TheAngryRaven/DovesDataLogger/CASE/VER_1/STEP/screen-cutout-template.STEP

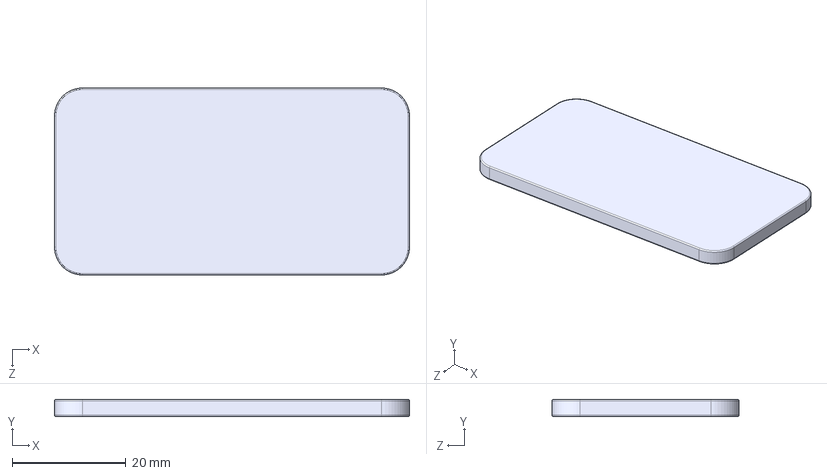
[picture p26: CAD file, 2026-03-16]
CASE/VER_1/STEP/screen-cutout-template.STEP
62.3 x 3.00 x 32.8 mm
