TheAngryRaven/DovesDataLogger/CASE/3MF/GPS-HOLDER.3MF

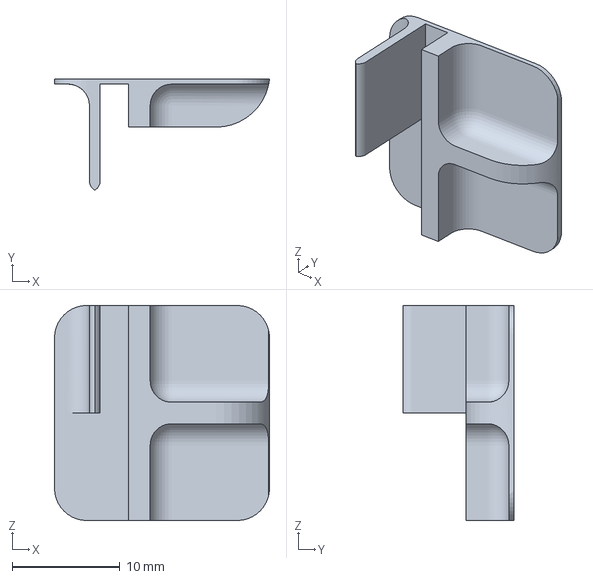
[picture p27: CAD file, 2026-07-27]
CASE/3MF/GPS-HOLDER.3MF
20.0 x 10.4 x 20.0 mm
