TheAngryRaven/DovesDataLogger/CASE/VER_1/STEP/switch-cover.STEP

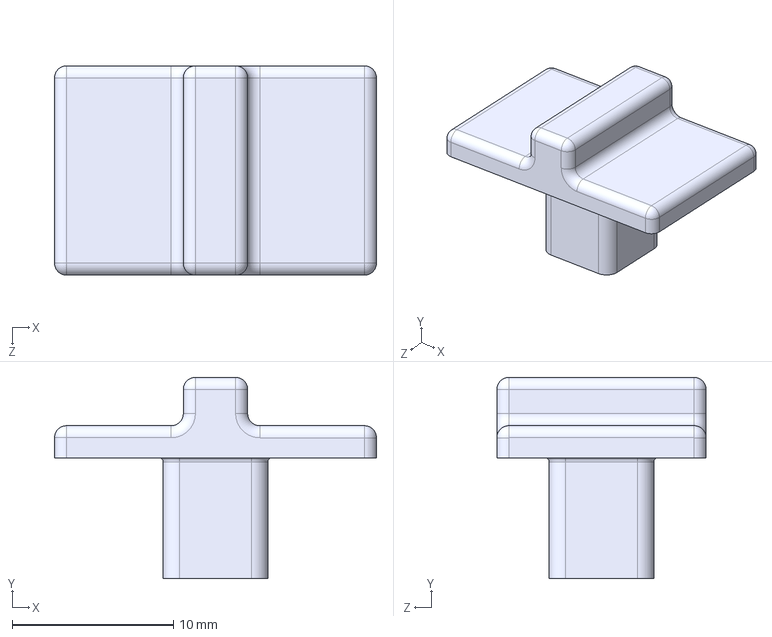
[picture p28: CAD file, 2026-03-16]
CASE/VER_1/STEP/switch-cover.STEP
20.0 x 12.5 x 13.0 mm
