TheAngryRaven/DovesDataLogger/CASE/3MF/cpu-lid.3MF

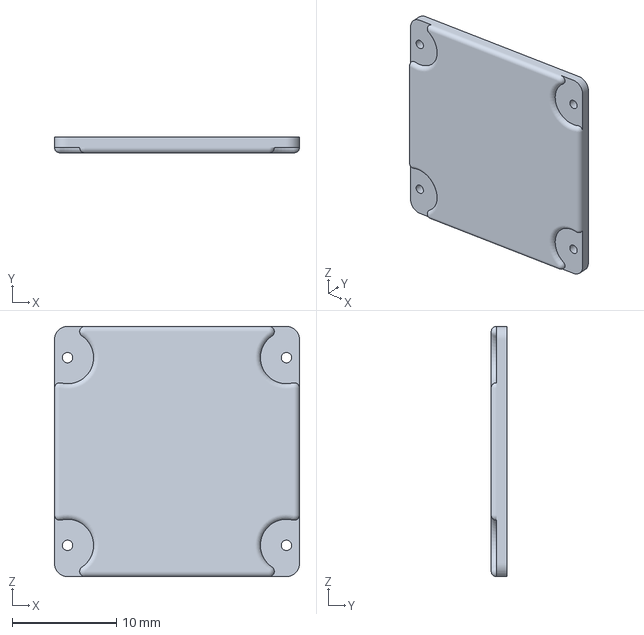
[picture p29: CAD file, 2026-07-27]
CASE/3MF/cpu-lid.3MF
23.5 x 1.50 x 24.0 mm
