TheAngryRaven/DovesDataLogger/CASE/VER_1/STEP/battery-lid.STEP

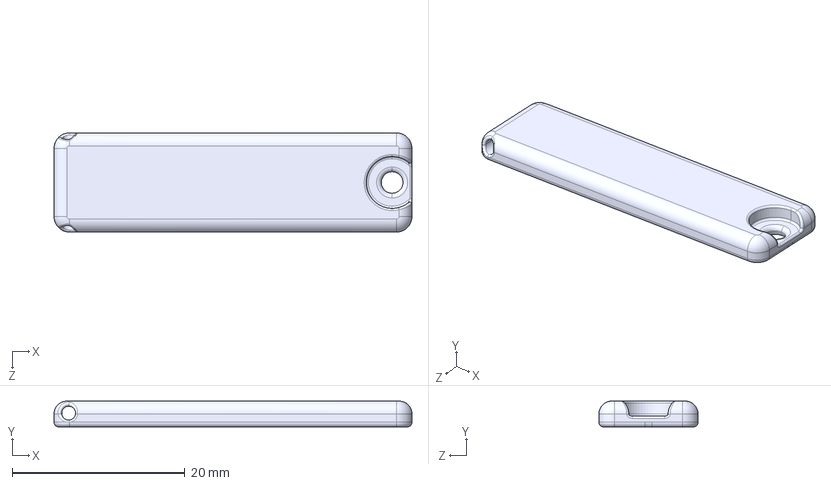
[picture p30: CAD file, 2026-03-16]
CASE/VER_1/STEP/battery-lid.STEP
41.5 x 3.00 x 11.5 mm
