TheAngryRaven/DovesDataLogger/CASE/3MF/diy-gps.3MF

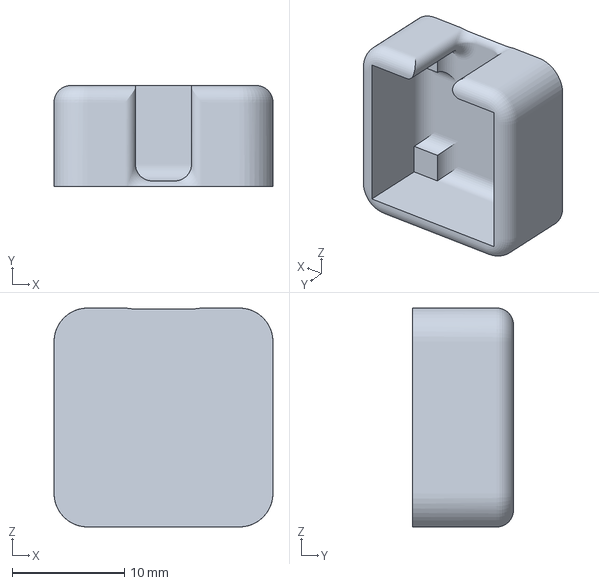
[picture p31: CAD file, 2026-07-27]
CASE/3MF/diy-gps.3MF
19.5 x 9.00 x 19.5 mm
