TheAngryRaven/DovesDataLogger/CASE/VER_1/STEP/sdcard.STEP

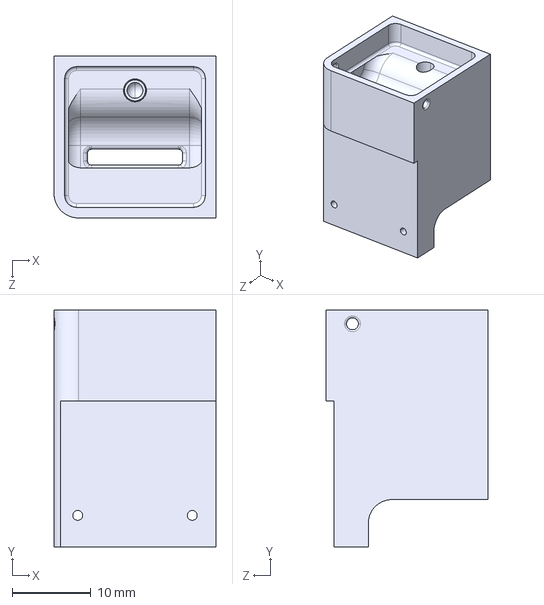
[picture p32: CAD file, 2026-03-16]
CASE/VER_1/STEP/sdcard.STEP
20.5 x 30.0 x 20.5 mm
