TheAngryRaven/DovesDataLogger/CASE/3MF/usbc_charger.3MF

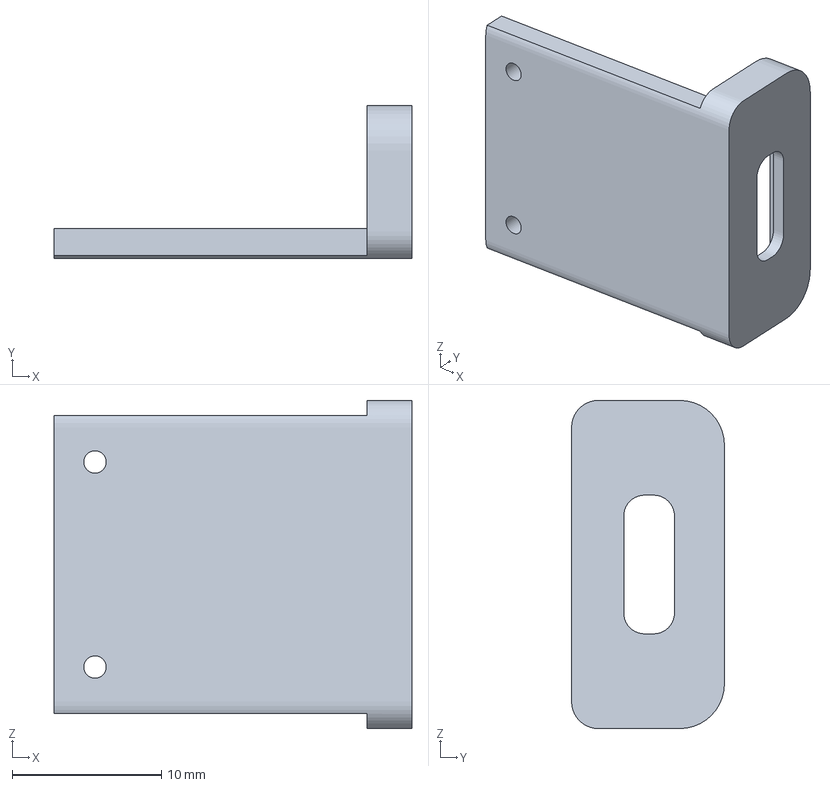
[picture p33: CAD file, 2026-07-27]
CASE/3MF/usbc_charger.3MF
24.0 x 10.2 x 22.0 mm
