TheAngryRaven/DovesDataLogger/CASE/VER_1/STEP/gps.STEP

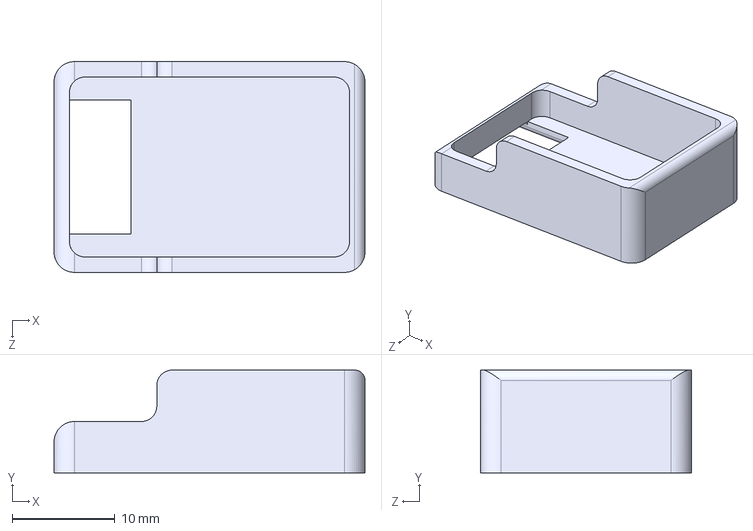
[picture p34: CAD file, 2026-03-16]
CASE/VER_1/STEP/gps.STEP
30.2 x 10.0 x 20.5 mm
