TheAngryRaven/DovesDataLogger/CASE/3MF/cpu.3MF

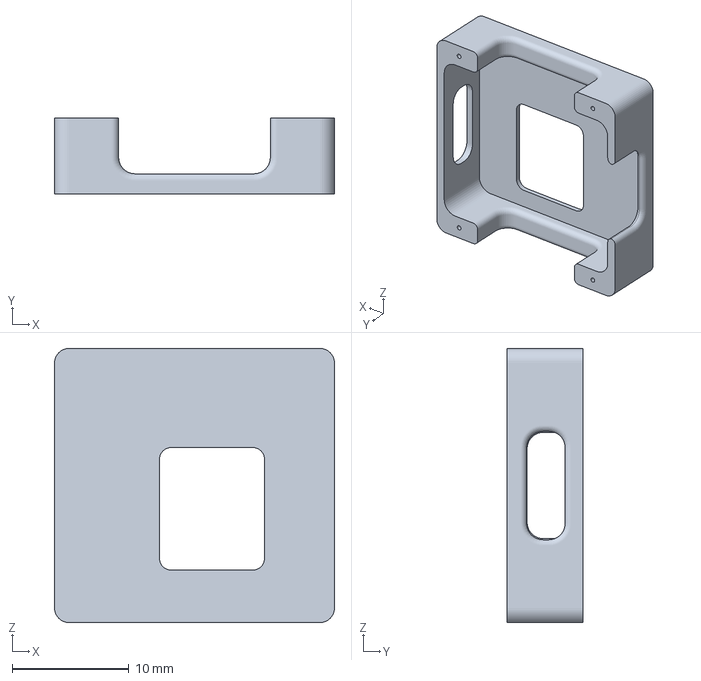
[picture p35: CAD file, 2026-07-27]
CASE/3MF/cpu.3MF
24.0 x 6.55 x 23.5 mm
