TheAngryRaven/DovesDataLogger/BirdsEye/gps_functions.ino

///////////////////////////////////////////
// GPS MODULE
// GPS time functions, configuration, setup, main loop, and frame rate
// Uses SparkFun u-blox GNSS v3 library with UBX PVT binary protocol
///////////////////////////////////////////

#include "gps_functions.h"
#include "gps_stats.h"
#include "gps_time.h"
#include "gps_validation.h"
#include "nan_bits.h"
#include "sat_bars.h"

///////////////////////////////////////////
// GPS SERIAL BUFFER — two buffers, two failure modes
//
// UARTE0 (per-byte ISR, NVIC prio 3) → core RingBuffer (256 B via the
// SERIAL_BUFFER_SIZE build flag; project.h asserts it) → TIMER3 ISR
// (prio 3, every GPS_DRAIN_INTERVAL_US) → this 4 KB ring → SparkFun
// library via GpsBufferedStream on the main loop.
//
// Downstream stalls (SD garbage collection blocks the main loop
// 100 ms–2 s): the 4 KB ring buffers ~1.6 s of stream while TIMER3
// keeps draining — the original reason this ISR exists.
//
// Upstream deferral (SoftDevice radio ISRs at prio 0–2 preempt both
// prio-3 ISRs): only the CORE ring absorbs bytes until TIMER3 gets to
// run. 256 B ≈ 44 ms of line rate at 57600 baud, so radio activity
// (SensorEgg scan windows, camera connection events) has huge margin
// before a byte is lost. Both overflow points are counted — see the
// gpsStats* accessors and the GPS debug page.
///////////////////////////////////////////

// Forward-declare ISR with C linkage BEFORE Arduino's preprocessor
// auto-generates a C++ prototype (which would conflict with extern "C").
extern "C" void TIMER3_IRQHandler(void);

#define GPS_RX_BUF_SIZE 4096
static uint8_t gpsRxBuf[GPS_RX_BUF_SIZE];
static volatile uint16_t gpsRxHead = 0;  // Written by ISR only
static volatile uint16_t gpsRxTail = 0;  // Read by main loop only (via gpsStream)
static volatile bool gpsTimerActive = false;

// Serial-pipeline health counters (monotonic since boot, read via the
// gpsStats*() accessors, shown on the GPS debug page). ISR writes are a
// few cycles each; no SVCs, no floats.
static volatile uint32_t gpsRingFullEvents = 0;   // 4KB ring full at drain time
static volatile uint32_t gpsIsrLatencyMaxUs = 0;  // worst TIMER3 fire→entry deferral
static volatile uint16_t gpsDrainMaxBytes = 0;    // biggest single-fire drain burst
static volatile uint32_t gpsCoreSatEvents = 0;    // drain burst filled the core RX ring
static gps_stats::DropMonitor gpsDropMonitor;     // main-loop only (frame-rate window)

// Stream wrapper: SparkFun library reads from our 4KB buffer instead of Serial1.
// Before the timer ISR is started (during GPS_SETUP), reads pass through to
// GPS_SERIAL directly so that myGNSS.begin() can communicate with the module.
class GpsBufferedStream : public Stream {
public:
  int available() override {
    if (!gpsTimerActive) return GPS_SERIAL.available();
    return (GPS_RX_BUF_SIZE + gpsRxHead - gpsRxTail) % GPS_RX_BUF_SIZE;
  }
  int read() override {
    if (!gpsTimerActive) return GPS_SERIAL.read();
    if (gpsRxHead == gpsRxTail) return -1;
    uint8_t c = gpsRxBuf[gpsRxTail];
    gpsRxTail = (gpsRxTail + 1) % GPS_RX_BUF_SIZE;
    return c;
  }
  int peek() override {
    if (!gpsTimerActive) return GPS_SERIAL.peek();
    if (gpsRxHead == gpsRxTail) return -1;
    return gpsRxBuf[gpsRxTail];
  }
  size_t write(uint8_t c) override {
    return GPS_SERIAL.write(c);
  }
  size_t write(const uint8_t *buffer, size_t size) override {
    return GPS_SERIAL.write(buffer, size);
  }
  void flush() override {
    GPS_SERIAL.flush();
  }
};

static GpsBufferedStream gpsStream;

// Timer3 ISR: drains Serial1 into our 4KB buffer every ~10ms.
// Single-producer (ISR writes gpsRxHead), single-consumer (main loop
// reads gpsRxTail via gpsStream) — lock-free ring buffer.
//
// Brief __disable_irq() around each GPS_SERIAL read protects the UART
// driver's internal FIFO from concurrent access by the core's UARTE
// ISR (same NVIC priority 3 as this handler, so it can't preempt us —
// the guard covers it firing *between* our read calls). Each critical
// section is ~0.3µs — well within SoftDevice's 6µs safe window.
void TIMER3_IRQHandler(void) {
  if (NRF_TIMER3->EVENTS_COMPARE[0]) {
    NRF_TIMER3->EVENTS_COMPARE[0] = 0;
    // The COMPARE0_CLEAR short zeroed the counter at the scheduled fire
    // time, so capturing now reads how long SoftDevice radio ISRs (the
    // only thing above priority 3) deferred this handler, in µs. If a
    // deferral swallows a whole period the reading wraps mod the period
    // — the drain/saturation counters below catch that case.
    NRF_TIMER3->TASKS_CAPTURE[1] = 1;
    uint32_t deferralUs = NRF_TIMER3->CC[1];
    if (deferralUs > gpsIsrLatencyMaxUs) gpsIsrLatencyMaxUs = deferralUs;
    uint16_t drained = 0;
    while (true) {
      __disable_irq();
      int c = GPS_SERIAL.available() ? GPS_SERIAL.read() : -1;
      __enable_irq();
      if (c < 0) break;

      uint16_t nextHead = (gpsRxHead + 1) % GPS_RX_BUF_SIZE;
      if (nextHead == gpsRxTail) {  // Buffer full, drop bytes
        gpsRingFullEvents++;
        break;
      }
      gpsRxBuf[gpsRxHead] = (uint8_t)c;
      gpsRxHead = nextHead;
      drained++;
    }
    if (drained > gpsDrainMaxBytes) gpsDrainMaxBytes = drained;
    // Draining a full core ring means it was saturated while we were
    // deferred — bytes may already have been dropped upstream (the
    // core's store_char discards silently on full).
    if (drained >= SERIAL_BUFFER_SIZE - 1) gpsCoreSatEvents++;
  }
}

void startGpsSerialTimer() {
  NRF_TIMER3->TASKS_STOP = 1;
  NRF_TIMER3->TASKS_CLEAR = 1;
  NRF_TIMER3->MODE = TIMER_MODE_MODE_Timer;
  NRF_TIMER3->BITMODE = TIMER_BITMODE_BITMODE_32Bit;
  NRF_TIMER3->PRESCALER = 4;              // 16MHz / 2^4 = 1MHz tick
  NRF_TIMER3->CC[0] = GPS_DRAIN_INTERVAL_US;  // drain period (see gps_config.h)
  NRF_TIMER3->SHORTS = TIMER_SHORTS_COMPARE0_CLEAR_Msk;
  NRF_TIMER3->INTENSET = TIMER_INTENSET_COMPARE0_Msk;
  NVIC_SetPriority(TIMER3_IRQn, 3);       // Below SoftDevice (0-2), above main loop
  NVIC_ClearPendingIRQ(TIMER3_IRQn);      // Clear stale pending interrupt from prior session
  NVIC_EnableIRQ(TIMER3_IRQn);
  gpsTimerActive = true;
  NRF_TIMER3->TASKS_START = 1;
  debugln(F("GPS serial buffer timer started"));
}

void stopGpsSerialTimer() {
  NRF_TIMER3->TASKS_STOP = 1;
  NRF_TIMER3->INTENCLR = TIMER_INTENCLR_COMPARE0_Msk;
  NVIC_DisableIRQ(TIMER3_IRQn);
  NVIC_ClearPendingIRQ(TIMER3_IRQn);      // Ensure no stale ISR fires after disable
  __DSB();                                 // ARM barrier: NVIC ops complete before flag update
  gpsTimerActive = false;
}

/**
  * @brief Returns the GPS time since midnight in milliseconds, or 0 if GPS unavailable.
  *        The pure math lives in gps_time::timeOfDayMs — this just plumbs through gpsData.
  */
unsigned long getGpsTimeInMilliseconds() {
  if (!gpsInitialized) return 0;
  return gps_time::timeOfDayMs(gpsData.hour, gpsData.minute,
                               gpsData.seconds, gpsData.milliseconds);
}

/**
  * @brief Converts GPS date/time to Unix timestamp in seconds. 0 if GPS unavailable.
  *        gpsData.year is the 2-digit year offset from 2000.
  */
unsigned long getGpsUnixTimestamp() {
  if (!gpsInitialized) return 0;
  return static_cast<unsigned long>(gps_time::unixTimestampSeconds(
      2000 + gpsData.year, gpsData.month, gpsData.day,
      gpsData.hour, gpsData.minute, gpsData.seconds));
}

/**
  * @brief Converts GPS date/time to Unix timestamp with millisecond precision.
  *        0 if GPS unavailable.
  */
unsigned long long getGpsUnixTimestampMillis() {
  if (!gpsInitialized) return 0;
  return gps_time::unixTimestampMillis(
      2000 + gpsData.year, gpsData.month, gpsData.day,
      gpsData.hour, gpsData.minute, gpsData.seconds, gpsData.milliseconds);
}

// PVT callback — called synchronously from checkCallbacks() when a new
// NAV-PVT message arrives.  Populates the shared gpsData struct and sets
// the gpsDataFresh flag so GPS_LOOP() knows to run lap-timer / logging.
void onPVTReceived(UBX_NAV_PVT_data_t *pvt) {
  // lat/lng stay double (see GpsData); the rest is single-precision with
  // reciprocal-constant multiplies — hardware FPU, no software-double
  // divides in this 25 Hz callback.
  gpsData.latitudeDegrees = pvt->lat / 1e7;
  gpsData.longitudeDegrees = pvt->lon / 1e7;
  gpsData.altitude = (float)pvt->hMSL * 0.001f;            // mm → meters
  gpsData.speed = (float)pvt->gSpeed * (1.0f / 514.444f);  // mm/s → knots
  gpsData.HDOP = (float)pvt->pDOP * 0.01f;                 // pDOP ≈ HDOP for track use
  gpsData.heading = (float)pvt->headMot * 1e-5f;           // deg * 1e-5 → degrees
  gpsData.horizontalAccuracy = (float)pvt->hAcc * 0.001f;  // mm → meters
  gpsData.satellites = pvt->numSV;
  // A fix is only trustworthy when the module also asserts gnssFixOK — a bare
  // fixType >= 2 can appear during convergence with garbage coordinates.
  gpsData.fix = (pvt->fixType >= 2) && (pvt->flags.bits.gnssFixOK != 0);
  // Time is only usable for naming/saving the log once the module reports the
  // date AND time AND a fully-resolved UTC. Before this, the module emits a
  // placeholder date (e.g. 2021-03-07) that must NOT drive file creation.
  gpsData.timeDateValid = (pvt->valid.bits.validDate != 0) &&
                          (pvt->valid.bits.validTime != 0);
  gpsData.timeResolved = (pvt->valid.bits.fullyResolved != 0);
  gpsData.timeValid = gpsData.timeDateValid && gpsData.timeResolved;
  gpsData.year = pvt->year - 2000;
  gpsData.month = pvt->month;
  gpsData.day = pvt->day;
  gpsData.hour = pvt->hour;
  gpsData.minute = pvt->min;
  gpsData.seconds = pvt->sec;
  gpsData.milliseconds = (pvt->iTOW % 1000);       // ms from GPS time-of-week

  gpsDataFresh = true;
  gpsPvtSequence++;  // monotonic; for consumers that run after GPS_LOOP()
  gpsFrameCounter++;
}

// NAV-SAT callback — fired by checkCallbacks() while status mode has
// NAV-SAT enabled. Snapshots per-satellite CNO (used-in-nav first,
// strongest first — rules in the host-tested sat_bars unit) for the GPS
// status page's signal bars.
void onNAVSATReceived(UBX_NAV_SAT_data_t *sat) {
  sat_bars::SatObs obs[64];
  uint8_t n = sat->header.numSvs;
  if (n > 64) n = 64;
  uint8_t used = 0;
  uint8_t tracked = 0;
  for (uint8_t i = 0; i < n; i++) {
    obs[i].cno = sat->blocks[i].cno;
    obs[i].used = (sat->blocks[i].flags.bits.svUsed != 0);
    if (obs[i].used) used++;
    if (obs[i].cno > 0) tracked++;  // hearing a signal, used in nav or not
  }
  gpsSatUsedCount = used;
  gpsSatTrackedCount = tracked;
  gpsSatCnoCount = (uint8_t)sat_bars::selectCnos(obs, n, gpsSatCnos,
                                                 sat_bars::kMaxSats);
}

// Register the message callbacks with the SparkFun library. Needed
// after every myGNSS.begin() — begin() resets library state, dropping
// previously registered callbacks.
static void gpsRegisterCallbacks() {
  // Runs under the armed WDT when re-registering after a baud recovery —
  // each call is a blocking VALSET/ACK exchange (see GPS_RECONFIGURE).
  wdtPet();
  myGNSS.setAutoPVTcallbackPtr(&onPVTReceived);
  wdtPet();
  if (gpsNavSatWanted) {
    myGNSS.setAutoNAVSATcallbackPtr(&onNAVSATReceived);
    wdtPet();
    // NAV-SAT frames are big (8 + 12*numSvs bytes); divide them down to
    // ~1 Hz instead of one per nav solution. Plenty for signal bars.
    myGNSS.setAutoNAVSATrate(GPS_NAV_RATE_STATUS_HZ);
    wdtPet();
  }
}

// Serial1 open-state guard for baud switches. The core's Uart::end()
// spin-waits on the TXSTOPPED + RXTO events, but a never-begun UARTE is
// disabled and ignores the STOPRX/STOPTX task writes — the events can
// never fire and end() loops forever. (end() has no _begun check; begin()
// does, and is a no-op on an open port, so a baud change NEEDS the end().)
// Track open state ourselves and only end() a port we actually opened.
static bool gpsSerialBegun = false;
static void gpsSerialRestart(unsigned long baud) {
  if (gpsSerialBegun) {
    GPS_SERIAL.end();
    delay(20);
  }
  GPS_SERIAL.begin(baud);
  gpsSerialBegun = true;
}

// The baud probe ladder. The module can be in ANY state at boot — every
// boot is a cold start now that sleep is System OFF:
//   (1) software backup mode holding a 57600 config (the normal wake),
//   (2) already-configured 57600 and running (MCU-only reset: reboot
//       combo, watchdog, OTA),
//   (3) factory 9600 NMEA (true cold power, or V_BCKP/VCC brownout).
// Sequence: backup-wake byte first (harmless if awake), probe 57600
// (the common warm case, ~instant), fall back to 9600 + rate switch,
// and only if all that fails pay a cold-boot delay and retry once.
// Caller owns gpsInitialized and the serial timer.
static bool gpsSetupProbe(bool coldRetry) {
  // Any UART activity on RX wakes u-blox from powerOff backup mode.
  gpsSerialRestart(GPS_BAUD_RATE);
  delay(50);
  GPS_SERIAL.write(0xFF);
  delay(100);

  // 57600 first — warm module answers immediately. Short maxWait: a
  // failing begin() is 3 internal ping retries back-to-back with no way
  // to pet the WDT in between (see GPS_PROBE_MAXWAIT_MS).
  wdtPet();
  if (myGNSS.begin(gpsStream, GPS_PROBE_MAXWAIT_MS)) {
    wdtPet();
    debugln(F("GPS found at 57600 (config retained)"));
    return true;
  }
  wdtPet();

  // 9600 fallback — factory default after a full config loss.
  debugln(F("GPS not at 57600, trying 9600..."));
  gpsSerialRestart(9600);
  delay(100);
  GPS_SERIAL.write(0xFF);  // wake again in case the first byte was eaten at the wrong baud
  delay(100);
  wdtPet();
  if (myGNSS.begin(gpsStream, GPS_PROBE_MAXWAIT_MS)) {
    wdtPet();
    debugln(F("GPS found at 9600, switching to 57600..."));
    myGNSS.setSerialRate(GPS_BAUD_RATE);
    delay(100);
    gpsSerialRestart(GPS_BAUD_RATE);
    delay(100);
    wdtPet();
    if (myGNSS.begin(gpsStream, GPS_PROBE_MAXWAIT_MS)) {
      wdtPet();
      debugln(F("GPS reconnected at 57600"));
      return true;
    }
    wdtPet();
    debugln(F("GPS lost after baud switch!"));
    return false;
  }
  wdtPet();

  // Neither baud answered. A module on true cold power may still be
  // booting — give it the boot time the old fixed delay(2250) paid up
  // front, then run the ladder once more.
  if (coldRetry) {
    debugln(F("GPS not detected, waiting for cold boot..."));
    for (int i = 0; i < 3; i++) {
      wdtPet();
      delay(500);
    }
    return gpsSetupProbe(false);
  }
  return false;
}

void GPS_SETUP() {
  gpsInitialized = false;  // Reset flag at start of setup

  #ifndef SIM
    debugln(F("ACTUAL GPS SETUP"));

    // gpsStream wraps GPS_SERIAL: before the timer starts, reads pass
    // through directly so myGNSS.begin() can communicate with the module.
    if (!gpsSetupProbe(/*coldRetry=*/true)) {
      debugln(F("ERROR: GPS not detected at any baud rate!"));
      return;  // Leave gpsInitialized = false; GPS_STATUS_RETRY_LOOP may re-probe
    }

    // Apply config at the current mode targets (boot = status mode:
    // 5 Hz + NAV-SAT for the GPS status page) and register callbacks.
    GPS_RECONFIGURE();
    gpsRegisterCallbacks();

    gpsInitialized = true;
    debugln(F("GPS initialized successfully (SparkFun UBX PVT)"));

    // Drain any remaining bytes from Serial1 into our buffer, then
    // start the timer ISR for continuous background serial drain.
    while (GPS_SERIAL.available()) {
      uint16_t nextHead = (gpsRxHead + 1) % GPS_RX_BUF_SIZE;
      if (nextHead == gpsRxTail) break;
      gpsRxBuf[gpsRxHead] = GPS_SERIAL.read();
      gpsRxHead = nextHead;
    }
    startGpsSerialTimer();

    // Arm the PVT-arrival watchdog for boot too: a begin() ping proves
    // the module answers, not that PVT flows. If nothing arrives within
    // 5 s, GPS_LOOP() runs GPS_BAUD_RECOVERY() — the "make sure we are
    // actually connected" check for a module in a weird state.
    gpsWakeTime = millis();
    gpsWakeValidated = false;
  #else
    // Simulator placeholder: no u-blox module to probe. The sim host
    // injects PVT data by calling onPVTReceived() directly, so there is
    // no serial/library setup to do here.
    debugln(F("SIM GPS SETUP"));
    gpsInitialized = true;
  #endif
}

// Bounded background re-detect for a GPS that failed GPS_SETUP().
// Called only while the GPS status page is up — each attempt blocks the
// UI ~2.5 s, so it's capped and spaced out. After the retries are spent
// the page shows a permanent "CHECK WIRING" and the device stays usable
// (race mode degrades gracefully without GPS).
static uint8_t gpsSetupRetryCount = 0;
static unsigned long gpsSetupLastRetry = 0;
#define GPS_SETUP_MAX_RETRIES 3
#define GPS_SETUP_RETRY_INTERVAL_MS 10000

bool gpsRetriesExhausted() {
  return !gpsInitialized && gpsSetupRetryCount >= GPS_SETUP_MAX_RETRIES;
}

void GPS_STATUS_RETRY_LOOP() {
  #ifndef SIM
  if (gpsInitialized) return;
  if (gpsSetupRetryCount >= GPS_SETUP_MAX_RETRIES) return;
  if (millis() - gpsSetupLastRetry < GPS_SETUP_RETRY_INTERVAL_MS) return;
  gpsSetupLastRetry = millis();
  gpsSetupRetryCount++;
  debug(F("GPS re-detect attempt "));
  debugln(gpsSetupRetryCount);

  if (!gpsSetupProbe(/*coldRetry=*/false)) return;

  GPS_RECONFIGURE();
  gpsRegisterCallbacks();
  gpsInitialized = true;
  gpsRxHead = 0;
  gpsRxTail = 0;
  startGpsSerialTimer();
  gpsWakeTime = millis();
  gpsWakeValidated = false;
  debugln(F("GPS re-detect succeeded"));
  #endif
}

void GPS_LOOP() {
  // Safety check: skip if GPS not initialized
  if (!gpsInitialized) {
    return;
  }

  // Process incoming UBX bytes and fire onPVTReceived() callback if a
  // complete PVT message has arrived.  The callback populates gpsData
  // and sets gpsDataFresh = true.
  myGNSS.checkUblox();
  myGNSS.checkCallbacks();

  // PVT arrival watchdog: after GPS_SETUP() or GPS_WAKE(), if no PVT data
  // arrives within 5 seconds, the module likely lost its config (V_BCKP
  // dropped → reverted to 9600 baud NMEA, or answered the begin() ping in
  // some odd state). Attempt baud recovery.
  if (!gpsWakeValidated) {
    if (gpsDataFresh) {
      // PVT arrived — module is alive and configured correctly
      gpsWakeValidated = true;
      debugln(F("GPS validated: PVT received"));
    } else if (millis() - gpsWakeTime >= 5000) {
      debugln(F("GPS validation FAILED: no PVT after 5s, attempting recovery"));
      if (GPS_BAUD_RECOVERY()) {
        // Recovery succeeded — restart the watchdog for validation
        gpsWakeTime = millis();
        debugln(F("GPS recovery succeeded, waiting for PVT..."));
      } else {
        // Recovery failed — give up, mark validated to stop retrying
        gpsWakeValidated = true;
        debugln(F("GPS recovery FAILED — GPS unavailable this session"));
      }
    }
  }

  if (gpsDataFresh) {
    gpsDataFresh = false;

    // Feed fresh GPS data into the active course/timer. courseManager and
    // sprintTimer are mutually exclusive by construction (mode follows the
    // detected track's folder) — exactly one branch runs per session.
    if (gpsData.fix && courseManager != nullptr) {
      double ltLat = gpsData.latitudeDegrees;
      double ltLng = gpsData.longitudeDegrees;
      double ltAlt = gpsData.altitude;
      double ltSpeed = gpsData.speed;

      courseManager->updateCurrentTime(getGpsTimeInMilliseconds());
      courseManager->loop(ltLat, ltLng, ltAlt, ltSpeed);
    } else if (gpsData.fix && sprintTimer != nullptr) {
      sprintTimer->updateCurrentTime(getGpsTimeInMilliseconds());
      sprintTimer->loop(gpsData.latitudeDegrees, gpsData.longitudeDegrees,
                        gpsData.altitude, gpsData.speed);
    }

  #ifdef SD_CARD_LOGGING_ENABLED
    // Determine if logging conditions are met.
    // File creation requires a VALID GPS time lock (validDate+validTime+
    // fullyResolved), not merely a non-zero day. Before the module resolves
    // real time it emits a placeholder date; creating a file from it produced
    // garbage-named logs (e.g. 20210307_0000.dovex) that collided every boot
    // and corrupted on reboot. With a real lock the module keeps time across
    // the V_BCKP backup, so this still fires within ~1 s of a warm wake.
    // While we wait, updateGpsLockHold() pins the user to the tachometer.
    // Data writing still requires gpsData.fix for valid coordinates.
    bool canWriteData = gpsData.fix && sdSetupSuccess && enableLogging && sdDataLogInitComplete;
    bool canCreateFile = sdSetupSuccess && enableLogging && !sdDataLogInitComplete && gpsData.timeValid;

    if (canWriteData) {

      /////////////////////////////////////////////////////////////////
      // Log every PVT update (~25Hz)

      // Snapshot GPS values for logging
      const double snapLat   = gpsData.latitudeDegrees;
      const double snapLng   = gpsData.longitudeDegrees;
      const double snapAlt   = gpsData.altitude;
      const double snapHdop  = gpsData.HDOP;
      const double snapSpeed = gpsData.speed;            // knots, for sanity
      const int    snapSats  = gpsData.satellites;
      const double snapSpeedMph = snapSpeed * 1.15078;

      // Reject obviously-corrupt samples (sats=0, Null Island, NaN/Inf,
      // out-of-range lat/lng/alt/hdop/speed). The rule set lives in
      // gps_validation::isSampleValid and is exercised by host tests.
      const gps_validation::GpsSample snapForCheck = {
          snapLat, snapLng, snapAlt, snapHdop, snapSpeedMph, snapSats};
      if (!gps_validation::isSampleValid(snapForCheck)) {
        // Skip this sample - data is not trustworthy
      } else {
        char csvLine[256];
        char latStr[24], lngStr[24], hdopStr[12], speedStr[16], altStr[16];
        char headingStr[12], hAccStr[12];

        dtostrf(snapLat, 1, 8, latStr);
        dtostrf(snapLng, 1, 8, lngStr);
        dtostrf(snapHdop, 1, 1, hdopStr);
        dtostrf(snapSpeedMph, 1, 2, speedStr);
        dtostrf(snapAlt, 1, 2, altStr);
        dtostrf(gpsData.heading, 1, 2, headingStr);
        dtostrf(gpsData.horizontalAccuracy, 1, 2, hAccStr);

        char accelXStr[12], accelYStr[12], accelZStr[12];
        dtostrf(accelX, 1, 3, accelXStr);
        dtostrf(accelY, 1, 3, accelYStr);
        dtostrf(accelZ, 1, 3, accelZStr);

#if BIRDSEYE_ENABLE_SENSOREGG
        // SensorEgg wireless EGT (Temp1) + cold junction (Junction1) +
        // aux intake-air temp (Temp2, v2 eggs), degC. Stale link or
        // egg-reported invalid -> literal "nan" so a dropout is a
        // visible gap, never a held flat line; a v1 egg logs Temp2 as
        // "nan" every row. These fields must NEVER cause the GPS row to
        // be skipped, so they are checked here (falling back to "nan")
        // instead of joining the strs[] reject-the-row walk below.
        // isNanF, not isnan: -Ofast folds isnan() to false. (These
        // columns previously survived that only because dtostrf(NaN)
        // emits "nan" and isNumericString rejects it into the same
        // fallback - luck, not design.)
        //
        // SENSOREGG BUILDS ONLY since plan 0013. Until then these three
        // columns were written on every channel, as the literal "nan"
        // on a stock image, so that the log shape never forked. That
        // rule is deliberately retired: three dead columns on every row
        // of every stock log paid for nothing. Readers key the data
        // section off its own CSV header line, where all three are
        // optional, so both shapes parse.
        char temp1Str[12], junc1Str[12], temp2Str[12];
        const float snapEgtC = sensoreggEgtC();
        const float snapJuncC = sensoreggJunctionC();
        const float snapAuxC = sensoreggAuxC();
        if (isNanF(snapEgtC)) {
          strcpy(temp1Str, "nan");
        } else {
          dtostrf(snapEgtC, 1, 1, temp1Str);
          if (!gps_validation::isNumericString(temp1Str, sizeof(temp1Str) - 1)) {
            strcpy(temp1Str, "nan");
          }
        }
        if (isNanF(snapJuncC)) {
          strcpy(junc1Str, "nan");
        } else {
          dtostrf(snapJuncC, 1, 1, junc1Str);
          if (!gps_validation::isNumericString(junc1Str, sizeof(junc1Str) - 1)) {
            strcpy(junc1Str, "nan");
          }
        }
        if (isNanF(snapAuxC)) {
          strcpy(temp2Str, "nan");
        } else {
          dtostrf(snapAuxC, 1, 1, temp2Str);
          if (!gps_validation::isNumericString(temp2Str, sizeof(temp2Str) - 1)) {
            strcpy(temp2Str, "nan");
          }
        }
#endif  // BIRDSEYE_ENABLE_SENSOREGG

        // dtostrf() can produce garbage (empty, too-long, non-numeric) on
        // some BSPs when given NaN/Inf even though the sample passed
        // validation. Walk every formatted string and reject the row if
        // any look wrong.
        bool stringsValid = true;
        const char* strs[] = {latStr, lngStr, hdopStr, speedStr, altStr,
                              headingStr, hAccStr, accelXStr, accelYStr, accelZStr};
        for (size_t i = 0; i < sizeof(strs)/sizeof(strs[0]) && stringsValid; i++) {
          if (!gps_validation::isNumericString(strs[i], 20)) {
            stringsValid = false;
          }
        }

        if (!stringsValid) {
          // dtostrf produced garbage - skip this entry silently
        } else {
          // Arduino lacks %llu in printf; format the 64-bit timestamp
          // ourselves into a stack buffer, then splice via %s.
          char timestampStr[24];
          gps_time::u64ToDecimalString(getGpsUnixTimestampMillis(),
                                        timestampStr, sizeof(timestampStr));

          // The two row shapes. Keep them adjacent: they and the CSV
          // header below are the only three places the column list
          // exists, and they have to agree.
#if BIRDSEYE_ENABLE_SENSOREGG
          snprintf(csvLine, sizeof(csvLine), "%s,%d,%s,%s,%s,%s,%s,%s,%s,%d,%s,%s,%s,%s,%s,%s",
                   timestampStr, snapSats, hdopStr, latStr, lngStr,
                   speedStr, altStr, headingStr, hAccStr,
                   tachLastReported, accelXStr, accelYStr, accelZStr,
                   temp1Str, junc1Str, temp2Str);
#else
          snprintf(csvLine, sizeof(csvLine), "%s,%d,%s,%s,%s,%s,%s,%s,%s,%d,%s,%s,%s",
                   timestampStr, snapSats, hdopStr, latStr, lngStr,
                   speedStr, altStr, headingStr, hAccStr,
                   tachLastReported, accelXStr, accelYStr, accelZStr);
#endif

          size_t written = dataFile.println(csvLine);
          if (written == 0) {
            // A write failed mid-session. Don't fault — keep racing so lap
            // timing / RPM / display stay live; just stop logging for this
            // session (closing cleanly rather than truncating-and-restarting
            // the same-minute filename).
            debugln(F("SD write failed - stopping logging, race continues"));
            enableLogging = false;
            sdDataLogInitComplete = false;
            // Try to salvage the session's lap times / metadata into the
            // reserved header before closing. A write failure here usually
            // means a flaky card, so this may also fail — but when it
            // succeeds the lap list survives instead of being lost with the
            // session. writeDovexHeader() no-ops if the file isn't open.
            writeDovexHeader();
            dataFile.close();
            releaseSDAccess(SD_ACCESS_LOGGING);
          }
        }
      }
      /////////////////////////////////////////////////////////////////

      // Flush periodically to avoid data loss - every 10 seconds
      if (millis() - lastCardFlush > 10000) {
        lastCardFlush = millis();
        dataFile.flush();
      }
    } else if (canCreateFile && millis() - lastLogCreateAttempt >= 1000) {
      // Throttle open attempts to once per second so a problem card can't
      // churn SPI at 25 Hz. We never fault out of race mode here — if the
      // file can't be created we simply keep waiting (the user stays on the
      // tachometer via the GPS-lock hold) and retry next second.
      lastLogCreateAttempt = millis();
      debugln(F("Attempt to initialize logfile"));

      if (!acquireSDAccess(SD_ACCESS_LOGGING)) {
        // Another subsystem holds the card (BLE/replay). Don't fault — just
        // retry on the next throttled pass once it releases.
        debugln(F("Cannot start logging - SD card busy, will retry"));
      } else {
        char dataFileName[80];

        // DOVEX filename: 20YYMMDD_HHMM.dovex
        snprintf(dataFileName, sizeof(dataFileName),
                 "20%02d%02d%02d_%02d%02d.dovex",
                 gpsData.year, gpsData.month, gpsData.day,
                 gpsData.hour, gpsData.minute);

        debug(F("dataFileName: ["));
        debug(dataFileName);
        debugln(F("]"));

        dataFile.open(dataFileName, O_CREAT | O_WRITE | O_TRUNC);

        if (!dataFile) {
          // Open failed — do NOT fault out of race mode. Release the card and
          // leave logging pending; updateGpsLockHold() keeps the user on the
          // tachometer and we retry on the next throttled pass.
          debugln(F("Error opening log file - will retry"));
          releaseSDAccess(SD_ACCESS_LOGGING);
        } else {
          // DOVEX: pre-fill header region with newlines so the FAT clusters
          // for it are allocated up front; the metadata header is written
          // back into this region at session end.
          char padBuf[64];
          memset(padBuf, '\n', sizeof(padBuf));
          bool prefillOk = true;
          for (uint32_t i = 0; i < DOVEX_HEADER_SIZE; i += sizeof(padBuf)) {
            uint32_t toWrite = min((uint32_t)sizeof(padBuf), DOVEX_HEADER_SIZE - i);
            // Verify each write landed. On a card dropping sectors mid-init,
            // an unchecked short write would leave a truncated header region
            // but we'd still mark logging ready and stream rows into garbage.
            if (dataFile.write(padBuf, toWrite) != toWrite) {
              prefillOk = false;
              break;
            }
          }
          if (!prefillOk) {
            debugln(F("Header pre-fill write failed - aborting log init, will retry"));
            dataFile.close();
            releaseSDAccess(SD_ACCESS_LOGGING);
          } else {
            // Cursor is now at exactly DOVEX_HEADER_SIZE.
            // The trailing Temp1/Junction1/Temp2 columns exist only on a
            // SensorEgg build (plan 0013) — must match the two row
            // shapes in the write path above.
#if BIRDSEYE_ENABLE_SENSOREGG
            dataFile.println(F("timestamp,sats,hdop,lat,lng,speed_mph,altitude_m,heading_deg,h_acc_m,rpm,accel_x,accel_y,accel_z,Temp1,Junction1,Temp2"));
#else
            dataFile.println(F("timestamp,sats,hdop,lat,lng,speed_mph,altitude_m,heading_deg,h_acc_m,rpm,accel_x,accel_y,accel_z"));
#endif
            debugln(F("CSV header written"));
            sdDataLogInitComplete = true;
          }
        }
      }
    }
  #endif

    // Update display speed with fresh PVT data
    gps_speed_mph = gpsData.speed * 1.15078;
  } // end if (gpsDataFresh)
}

void GPS_SLEEP() {
  if (!gpsInitialized) return;
  stopGpsSerialTimer();  // Stop serial drain ISR during sleep (saves power)
  myGNSS.powerOff(0);   // 0 = indefinite sleep until woken
}

/**
 * @brief Re-apply all GPS module configuration via VALSET.
 *
 * The SAM-M10Q has no flash — all config lives in volatile RAM. If V_BCKP
 * drops during backup mode (battery sag, loose connector, cranking brownout),
 * the module reverts to factory defaults (9600 baud, NMEA, 1Hz). This
 * function re-applies the full configuration at the CURRENT mode targets
 * (gpsNavRateTarget / gpsNavSatWanted) so wake/recovery paths re-assert
 * whatever mode we're actually in instead of clobbering it. It's fast
 * (~50ms total) and idempotent — safe to call even if config was retained.
 */
void GPS_RECONFIGURE() {
  // The stream restarts around a reconfigure (wake/recovery paths) —
  // discard the frame-rate window in progress so the gap isn't
  // miscounted as dropped frames.
  gps_stats::noteRateChange(gpsDropMonitor);
  // This runs under the armed ~4 s WDT when called from GPS_BAUD_RECOVERY
  // or GPS_WAKE. Each call below is a VALSET + ACK wait that can block up
  // to ~1.1 s on a module that answers the connection ping but responds
  // slowly (cold acquisition, marginal wiring) — 8 of them back-to-back
  // is a guaranteed watchdog reset. Pet between every exchange.
  wdtPet();
  myGNSS.setUART1Output(COM_TYPE_UBX);
  wdtPet();
  myGNSS.setNavigationFrequency(gpsNavRateTarget);
  wdtPet();
  myGNSS.setDynamicModel(DYN_MODEL_AUTOMOTIVE);
  wdtPet();
  myGNSS.enableGNSS(true, SFE_UBLOX_GNSS_ID_GPS);
  wdtPet();
  myGNSS.enableGNSS(false, SFE_UBLOX_GNSS_ID_SBAS);
  wdtPet();
  myGNSS.enableGNSS(false, SFE_UBLOX_GNSS_ID_GALILEO);
  wdtPet();
  myGNSS.enableGNSS(false, SFE_UBLOX_GNSS_ID_BEIDOU);
  wdtPet();
  myGNSS.enableGNSS(false, SFE_UBLOX_GNSS_ID_GLONASS);
  wdtPet();
  if (!gpsNavSatWanted) {
    myGNSS.setAutoNAVSAT(false);  // no periodic NAV-SAT output in race mode
    wdtPet();
  }
  debugln(F("GPS config re-applied (VALSET)"));
}

/**
 * @brief Switch to status mode: GPS_NAV_RATE_STATUS_HZ nav solutions with
 *        NAV-SAT output for the GPS status page's signal bars. This is
 *        also the boot default (the targets initialize to it).
 */
void gpsEnterStatusMode() {
  gpsNavRateTarget = GPS_NAV_RATE_STATUS_HZ;
  gpsNavSatWanted = true;
  gps_stats::noteRateChange(gpsDropMonitor);
  if (!gpsInitialized) return;
  myGNSS.setNavigationFrequency(gpsNavRateTarget);
  myGNSS.setAutoNAVSATcallbackPtr(&onNAVSATReceived);
  myGNSS.setAutoNAVSATrate(GPS_NAV_RATE_STATUS_HZ);  // ~1 Hz NAV-SAT frames
  debugln(F("GPS status mode (5Hz + NAV-SAT)"));
}

/**
 * @brief Switch to race mode: GPS_NAV_RATE_HZ PVT-only. Called when the
 *        GPS status page exits — this is the steady state for the menu
 *        and racing.
 */
void gpsEnterRaceMode() {
  gpsNavRateTarget = GPS_NAV_RATE_HZ;
  gpsNavSatWanted = false;
  gps_stats::noteRateChange(gpsDropMonitor);
  gpsSatCnoCount = 0;  // stale bars must not outlive the mode
  gpsSatUsedCount = 0;
  gpsSatTrackedCount = 0;
  if (!gpsInitialized) return;
  myGNSS.setAutoNAVSAT(false);
  myGNSS.setNavigationFrequency(gpsNavRateTarget);
  debugln(F("GPS race mode (25Hz PVT-only)"));
}

/**
 * @brief Attempt to recover GPS communication when module has reverted to 9600 baud.
 *
 * If V_BCKP was lost during backup, the module reverts to 9600 baud.
 * Our UART is at 57600 so communication is broken. This function:
 * 1. Stops the serial timer (switch to direct Serial1 mode)
 * 2. Tries to talk at 57600 first (maybe module is fine)
 * 3. If that fails, switches to 9600, sends baud change command, switches back
 * 4. Re-applies full config and restarts the serial timer
 *
 * @return true if communication was recovered, false if unrecoverable
 */
bool GPS_BAUD_RECOVERY() {
  debugln(F("GPS baud recovery: attempting..."));

  // This path runs from GPS_LOOP() under the armed ~4 s hardware watchdog,
  // and it is the slowest thing in the firmware short of the OTA apply.
  // A failing myGNSS.begin() is 3 internal ping retries with no pet
  // opportunity in between, so every probe uses GPS_PROBE_MAXWAIT_MS
  // (3 x 550 ms = ~1.65 s worst case) and is bracketed by pets — against
  // a genuinely hung module that out-waits the WDT → reset → re-setup →
  // recovery → reset boot loop, the one path built to revive a sick GPS
  // must not trip the watchdog.
  wdtPet();

  // Stop timer so GpsBufferedStream passes through to Serial1 directly.
  // The SparkFun library needs direct serial access for begin()/setSerialRate().
  stopGpsSerialTimer();

  // First: try at current baud — module might be fine, just slow to start
  if (myGNSS.begin(gpsStream, GPS_PROBE_MAXWAIT_MS)) {
    wdtPet();
    debugln(F("GPS baud recovery: module responding at 57600"));
    GPS_RECONFIGURE();       // pets internally per VALSET exchange
    gpsRegisterCallbacks();  // begin() resets library state; pets internally
    gpsRxHead = 0;
    gpsRxTail = 0;
    startGpsSerialTimer();
    return true;
  }

  // Module not responding at 57600 — try 9600 (factory default)
  debugln(F("GPS baud recovery: trying 9600..."));
  wdtPet();  // the first begin() just burned ~1.65 s of the 4 s budget
  GPS_SERIAL.end();
  delay(50);
  GPS_SERIAL.begin(9600);
  delay(100);

  if (myGNSS.begin(gpsStream, GPS_PROBE_MAXWAIT_MS)) {
    // Found at 9600 — switch it back to 57600
    debugln(F("GPS baud recovery: found at 9600, switching to 57600"));
    wdtPet();  // second begin() done; baud switch + final probe still ahead
    myGNSS.setSerialRate(GPS_BAUD_RATE);
    delay(100);
    GPS_SERIAL.end();
    delay(50);
    GPS_SERIAL.begin(GPS_BAUD_RATE);
    delay(100);
    wdtPet();

    if (myGNSS.begin(gpsStream, GPS_PROBE_MAXWAIT_MS)) {
      wdtPet();
      debugln(F("GPS baud recovery: reconnected at 57600"));
      GPS_RECONFIGURE();
      gpsRegisterCallbacks();
      gpsRxHead = 0;
      gpsRxTail = 0;
      startGpsSerialTimer();
      return true;
    }
    debugln(F("GPS baud recovery: lost after baud switch!"));
  } else {
    debugln(F("GPS baud recovery: not found at 9600 either"));
  }

  // Restore 57600 even on failure so other code doesn't break
  wdtPet();
  GPS_SERIAL.end();
  delay(50);
  GPS_SERIAL.begin(GPS_BAUD_RATE);
  delay(50);
  gpsRxHead = 0;
  gpsRxTail = 0;
  startGpsSerialTimer();
  return false;
}

void GPS_WAKE() {
  if (!gpsInitialized) return;

  // Clear stale state from before sleep / periodic checks
  gpsDataFresh = false;
  gpsData.fix = false;

  // Any UART activity on RX wakes u-blox from powerOff backup mode
  GPS_SERIAL.write(0xFF);
  delay(100);

  // Reset buffer pointers (stale data from before sleep is useless)
  gpsRxHead = 0;
  gpsRxTail = 0;

  startGpsSerialTimer();  // Resume serial drain ISR

  // Re-apply configuration in case module lost RAM during backup.
  // This is idempotent — if config was retained, these are no-ops.
  GPS_RECONFIGURE();

  myGNSS.checkUblox();

  // Start PVT arrival watchdog. GPS_LOOP() will validate within 5 seconds,
  // and trigger baud recovery if no PVT data arrives.
  gpsWakeTime = millis();
  gpsWakeValidated = false;
}

void calculateGPSFrameRate() {
  // calculate actual GPS fix frequency
  gpsFrameEndTime = millis();
  // Check if the update interval has passed
  if (gpsFrameEndTime - gpsFrameStartTime >= 1000) {
    unsigned long elapsed = gpsFrameEndTime - gpsFrameStartTime;
    // Calculate the frame rate (loops per second)
    gpsFrameRate = (float)gpsFrameCounter / (elapsed / 1000.0);
    // Feed the drop accounting: expected-vs-received against the
    // current nav-rate target (window math in the gps_stats pure unit).
    gps_stats::windowUpdate(gpsDropMonitor, gpsFrameCounter, elapsed,
                            gpsNavRateTarget);
    // Reset the loop counter and start time for the next interval
    gpsFrameCounter = 0;
    gpsFrameStartTime = millis();
  }
}

// Serial-pipeline health accessors (GPS debug page + GPS stats page).
uint32_t gpsStatsDroppedPvt() { return gpsDropMonitor.droppedTotal; }
uint32_t gpsStatsRingFullEvents() { return gpsRingFullEvents; }
uint32_t gpsStatsIsrLatencyMaxUs() { return gpsIsrLatencyMaxUs; }
uint16_t gpsStatsDrainMaxBytes() { return gpsDrainMaxBytes; }
uint32_t gpsStatsCoreSatEvents() { return gpsCoreSatEvents; }
