TheAngryRaven/DovesDataLogger/BirdsEye/project.h

#ifndef _DOVES_PROJECT_H
#define _DOVES_PROJECT_H

#include <stdint.h>

///////////////////////////////////////////
// DovesDataLogger - Project-Wide Types & Macros
//
// This header is included FIRST in BirdsEye.ino so that custom types
// are available before the Arduino preprocessor generates function
// prototypes from the other .ino module files.
///////////////////////////////////////////

///////////////////////////////////////////
// FIRMWARE VERSION
//
// Single source of truth for the *base* firmware version. Exposed over BLE
// via the Device Information Service (see bluetooth.ino) so a companion
// (DovesDataViewer) can compare it against the latest GitHub release and
// decide whether an OTA update is needed. Keep this in sync with the release
// git tag (tag v2.0.0 -> "2.0.0") and the CHANGELOG.
//
// Beta/nightly builds override it from the build flag: the beta workflow
// passes -DFIRMWARE_VERSION_OVERRIDE=<base>-beta.<gitsha> as a bare token —
// the stringizer below quotes it, so there is no shell quote-escaping to get
// wrong. A normal build (prod release, plain IDE, compile-sketch CI) leaves it
// undefined and uses the literal below.
///////////////////////////////////////////
#define _BE_STRINGIFY(x) #x
#define _BE_TOSTRING(x) _BE_STRINGIFY(x)
#ifdef FIRMWARE_VERSION_OVERRIDE
  #define FIRMWARE_VERSION _BE_TOSTRING(FIRMWARE_VERSION_OVERRIDE)
#else
  // The 4.1.0 release cut (matches the v4.1.0 tag). The webapp still keys
  // the track JSON budget off this — 8 KB at or above 3.2.0 — so never
  // stamp a build below that line again.
  #define FIRMWARE_VERSION "4.1.0"
#endif

///////////////////////////////////////////
// BUILD FEATURE FLAGS
//
// Each is a plain 0/1 macro with a #ifndef default, so a build can force
// either state explicitly (-DFLAG=1 / -DFLAG=0). A bare -DFLAG also works
// (the compiler defines it as 1). Test them with #if, never #ifdef — a
// deliberate -DFLAG=0 must lose to the feature being off.
///////////////////////////////////////////

// ---- Onboard (XIAO) battery charging ----
//
// 0 (default — master, beta and release all ship this): the firmware keeps
// its hands off the BQ25100. HICHG is never driven, so the onboard charger
// stays at its ~50 mA default and an EXTERNAL charging circuit owns the
// battery. USB is then a host/data connection rather than a charge session:
// a VBUS wake boots normally instead of shortcutting to the charge screen,
// and the main menu no longer pulls itself down after
// USB_MENU_CHARGE_IDLE_MS just because a cable is plugged in.
//
// 1: the pre-3.0.1 behavior — hold HICHG high for ~100 mA fast charge and
// run the charging UX built around it.
//
// NOTE (independent of this flag): with VBUS present, shutdown still parks
// in a display-off loop instead of entering System OFF. VBUS is an
// always-armed System OFF wake source on the nRF52840, so powering down
// with the cable still in risks an immediate wake-reset loop. The park is a
// hardware constraint, not a charging feature.
#ifndef BIRDSEYE_ENABLE_ONBOARD_CHARGING
  #define BIRDSEYE_ENABLE_ONBOARD_CHARGING 0
#endif

// ---- SensorEgg wireless EGT (BLE observer, proof of concept) ----
//
// 0 (default — master and release): the whole POC is compiled out. No
// passive scanner, no Temp1 race page, and BLE goes back to coming up
// lazily on first camera/transfer use instead of at boot. The DOVEX
// Temp1/Junction1 columns are still written (as `nan`) so the log format is
// identical across channels.
//
// 1 (the beta channel passes -DBIRDSEYE_ENABLE_SENSOREGG=1): scanner,
// display page and live readings all present.
#ifndef BIRDSEYE_ENABLE_SENSOREGG
  #define BIRDSEYE_ENABLE_SENSOREGG 0
#endif

// ---- NeoPixel strip (11 px: 2 status + 9-px pace/RPM strip) ----
//
// 1 (default — master, beta and release all ship this as of 4.1.0): the
// strip is a CORE feature, present in every image so a logger works the
// moment someone wires LEDs to it. On first boot NEOPIXEL_SETUP()
// converts the NFC pads to GPIO by programming UICR->NFCPINS and
// self-resets once so the pin latch takes effect. After that: pin 30 =
// boost converter EN, pin 31 = WS2812 data. See plan 0006 and neopixel.h.
//
// KNOW WHAT THIS COSTS, because it is charged to every unit in the field,
// not just the ones with LEDs on them. The UICR write is ONE-WAY — undoing
// it needs a full chip erase, i.e. a bootloader reflash over USB — so the
// first boot after updating to 4.1.0 permanently spends the NFC pads and
// reboots itself once, on every device, wired for LEDs or not. That was the
// deliberate 4.1.0 decision (NFC is not used on this hardware and the pads
// are otherwise idle); it is recorded here rather than in a commit message
// because nothing about a later build can undo it.
//
// 0 (no shipped channel sets this; -DBIRDSEYE_ENABLE_NEOPIXEL=0 forces it):
// the subsystem is compiled out — no Adafruit_NeoPixel dependency, and on a
// board that has NOT already been converted the firmware never writes UICR
// and never drives pins 30/31. On one that HAS (it ran a flag-on build
// before), the stubs still hold the boost EN pin low, because a floating EN
// leaves the 5 V rail up through System OFF — see the #else block in
// neopixel.ino.
#ifndef BIRDSEYE_ENABLE_NEOPIXEL
  #define BIRDSEYE_ENABLE_NEOPIXEL 1
#endif

// ---- Main-loop CPU profiling (plan 0011) ----
//
// 0 (default — master and release): compiled out completely. The section
// brackets in loop() vanish (they are macros, not calls), no LOOP PROFILE
// page exists, and pin 30 goes on being the NeoPixel boost converter's EN
// line exactly as it always has.
//
// 1 (the beta channel passes -DBIRDSEYE_ENABLE_PROFILING=1): every
// subsystem call in loop() is timed, rolled up once a second onto the
// LOOP PROFILE race page, and pin 30 becomes a scope-readable profiling
// output. This exists to measure what a main-loop iteration actually
// costs on this hardware, as the input to the nRF52840-vs-nRF5340 board
// decision and to any "what would leaving the Arduino core buy us"
// comparison.
//
// KNOW WHAT THIS COSTS, and it is not free: a profiling build gives up
// firmware control of the 5 V boost rail. Pin 30 cannot be both EN and a
// profiling output, so the profiler takes it and the regulator is left at
// its hardware default (EN pulled up = on). NEOPIXEL_SETUP/SLEEP/WAKE
// stop driving EN, which means the rail — and the idle current of 11
// WS2812s — stays up through System OFF, where GPIO levels are retained
// and nothing else will pull it down. A profiling unit left asleep on a
// battery goes flat. This is a bench build; do not hand one to a driver.
// See profiling.h for the pin's wiring caveat and the timebase notes.
#ifndef BIRDSEYE_ENABLE_PROFILING
  #define BIRDSEYE_ENABLE_PROFILING 0
#endif

///////////////////////////////////////////
// BOARD VARIANT
//
// Identifies which XIAO nRF52840 this image targets so the companion can
// fetch the matching OTA package. Reported over BLE as part of the DIS
// model string ("BirdsEye-" FIRMWARE_VARIANT), which equals the release
// asset prefix (BirdsEye-sense.zip / BirdsEye-nonsense.zip) so the webapp
// can map model -> download directly.
//
// Resolution order:
//   1. The build workflows pass -DBIRDSEYE_BOARD_SENSE / -DBIRDSEYE_BOARD_NONSENSE
//      per FQBN — these always win.
//   2. A plain Arduino IDE build passes no such flag, but the Seeeduino core
//      defines ARDUINO_<build.board> from the Tools -> Board selection
//      (ARDUINO_Seeed_XIAO_nRF52840_Sense vs ARDUINO_Seeed_XIAO_nRF52840), so
//      we derive the variant from the board you actually picked — no manual
//      flag needed.
//   3. If nothing matches (some other core / unknown board), default to
//      "sense" (the primary board).
// A wrong label only affects which OTA asset the companion offers — the images
// share the MCU/SoftDevice, the non-Sense image boots fine on a Sense board and
// vice-versa, and accelerometer presence is auto-detected at runtime regardless
// of this flag — so a mislabel never bricks.
///////////////////////////////////////////
#if defined(BIRDSEYE_BOARD_NONSENSE)
  #define FIRMWARE_VARIANT "nonsense"
#elif defined(BIRDSEYE_BOARD_SENSE)
  #define FIRMWARE_VARIANT "sense"
#elif defined(ARDUINO_Seeed_XIAO_nRF52840_Sense)
  #define FIRMWARE_VARIANT "sense"
#elif defined(ARDUINO_Seeed_XIAO_nRF52840)
  #define FIRMWARE_VARIANT "nonsense"
#else  // unknown board / core — fall back to the primary variant
  #define FIRMWARE_VARIANT "sense"
#endif

///////////////////////////////////////////
// BUILD-FLAG CONTRACT: GPS UART BUFFER
//
// The core's Serial1 RX ring must be 256 B (stock is 64 B, #ifndef-
// guarded in the BSP's RingBuffer.h). SoftDevice radio interrupts
// (unmaskable, prio 0–2) defer the TIMER3 GPS drain ISR (prio 3); at
// 57600 baud the stock 64 B ring gives only ~1 ms of deferral slack
// before bytes are silently dropped and 25 Hz PVT frames are lost —
// the exact field regression the drop counters were built to catch.
// A silently under-buffered build would reintroduce it, so fail loud.
//
// CI passes -DSERIAL_BUFFER_SIZE=256 (all three workflows). For a
// local Arduino IDE / arduino-cli build, see CONTRIBUTING.md
// ("Local build flags") — one-time setup via platform.local.txt or
// --build-property.
///////////////////////////////////////////
#ifndef SIM
static_assert(SERIAL_BUFFER_SIZE >= 256,
              "Build with -DSERIAL_BUFFER_SIZE=256 (see CONTRIBUTING.md, "
              "'Local build flags') — the stock 64 B Serial1 ring drops GPS "
              "bytes under BLE radio load.");
#endif

///////////////////////////////////////////
// DEBUG MACROS
///////////////////////////////////////////

#ifdef HAS_DEBUG
#define debugln Serial.println
#define debug Serial.print
#else
inline void dummy_debug(...) {
}
#define debug dummy_debug
#define debugln dummy_debug
#endif

///////////////////////////////////////////
// PROJECT LIMITS
// Defined here so structs below can reference them.
// These were previously in BirdsEye.ino — moved here for
// visibility in project-wide types.
///////////////////////////////////////////
#define MAX_LOCATIONS 200
#define MAX_LOCATION_LENGTH 13  // 13 is old DOS format for FAT16
#define MAX_LAYOUTS 10
#define MAX_LAYOUT_LENGTH 15
#define DOVEX_HEADER_SIZE 1024  // Reserved header bytes in .dovex files (1 KB)
#define TRACK_DETECT_RADIUS_MILES 5.0  // Haversine threshold for live track detection

// Shutdown (System OFF) constants
#define SLEEP_IDLE_TIMEOUT_MS     300000   // 5 min menu idle -> auto-shutdown
#define SLEEP_LONG_PRESS_MS       5000     // 5s hold for shutdown/reboot combos
#define CHARGE_DISPLAY_TIMEOUT_MS 10000    // Show charging screen for 10s then display off
#define USB_MENU_CHARGE_IDLE_MS   60000    // USB on menu: charging loop after 60s of no buttons
// Auto-race must not hijack a deliberate navigation. Leaving a page drops the
// user on the main menu, and above the speed/RPM trigger the very next loop
// iteration would convert that into "start racing" — the menu never even gets
// drawn. Require the menu to have been settled (no arrival, no button) this
// long first. Only bites right after an interaction: the normal auto-race case
// (parked on the menu, then drive off) has been quiet for minutes.
#define AUTO_RACE_MENU_GRACE_MS   3000

///////////////////////////////////////////
// BLE RADIO OWNERSHIP
// The one SoftDevice (single advert set + single peripheral connection
// slot) is shared between the file-transfer service (bluetooth.ino) and
// the camera remote (camera_ble.ino). bleOwner (defined in BirdsEye.ino,
// documented in bluetooth.h) records which subsystem currently owns the
// advert set, so the shared connect/disconnect callbacks can route a
// peer to the right module.
///////////////////////////////////////////
enum BleOwner : uint8_t {
  BLE_OWNER_NONE = 0,      // radio idle — nobody advertising
  BLE_OWNER_TRANSFER = 1,  // file-transfer page (BLE_SETUP/BLE_STOP)
  BLE_OWNER_CAMERA = 2,    // camera remote (camera_ble)
};

///////////////////////////////////////////
// RACE SESSION ENTRY CAUSE
// How the current race session was started (set by startRaceSession in
// BirdsEye.ino, RACE_ENTRY_NONE outside a session). Manual/speed sessions
// have no engine signal, so the camera lifecycle and the auto-idle rule
// key off this instead of RPM: they record from session start and end
// after 5 min below 5 mph, where tach sessions keep the RPM-driven rules.
///////////////////////////////////////////
enum RaceEntryCause : uint8_t {
  RACE_ENTRY_NONE = 0,    // no session active
  RACE_ENTRY_MANUAL = 1,  // main-menu Race select
  RACE_ENTRY_SPEED = 2,   // auto-race speed trip (>= 10 mph on the menu)
  RACE_ENTRY_TACH = 3,    // auto-race RPM trip, or tach-wake boot
};

///////////////////////////////////////////
// STRUCT DEFINITIONS
// Must be in a header so Arduino's auto-prototype generation
// can resolve these types in function signatures.
///////////////////////////////////////////

struct ButtonState {
  int pin = 0;
  bool pressed = false;           // Flag for "button was pressed" (consumed by handler)
  bool wasReleased = true;        // Edge detection: must release before next press
  unsigned long lastPressed = 0;
};

struct TrackLayout {
  double start_a_lat = 0.00;
  double start_a_lng = 0.00;
  double start_b_lat = 0.00;
  double start_b_lng = 0.00;

  // Sector 2 line data (optional)
  double sector_2_a_lat = 0.00;
  double sector_2_a_lng = 0.00;
  double sector_2_b_lat = 0.00;
  double sector_2_b_lng = 0.00;
  bool hasSector2 = false;

  // Sector 3 line data (optional)
  double sector_3_a_lat = 0.00;
  double sector_3_a_lng = 0.00;
  double sector_3_b_lat = 0.00;
  double sector_3_b_lng = 0.00;
  bool hasSector3 = false;

  // Sprint-only: the separate finish line (a run is start -> finish).
  double finish_a_lat = 0.00;
  double finish_a_lng = 0.00;
  double finish_b_lat = 0.00;
  double finish_b_lng = 0.00;
  bool hasFinish = false;

  // Sprint-only: sortable ISO-8601 creation stamp ("YYYY-MM-DDTHH:MM",
  // any prefix). Drives newest-course selection (sprint_select unit) —
  // autocross venues re-lay the course every event. Empty on circuit
  // courses and legacy files.
  char date_created[20] = "";
};

///////////////////////////////////////////
// TRACK MANIFEST (in-RAM index for proximity detection)
// Built during buildTrackList() at boot. Each entry stores
// the filename, a representative lat/lon from the first course, and
// which folder (= track kind) the file came from.
///////////////////////////////////////////

// Track kinds: which SD folder a manifest entry came from. Values mirror
// the host-tested sprint_select::Kind enum.
#define TRACK_KIND_CIRCUIT 0  // /TRACKS
#define TRACK_KIND_SPRINT  1  // /TRACKS/SPRINT

struct TrackManifestEntry {
  char filename[32];   // track filename without extension (matches locations[])
  double lat;          // first course's start_a_lat
  double lon;          // first course's start_a_lng
  uint8_t kind;        // TRACK_KIND_CIRCUIT / TRACK_KIND_SPRINT
};

///////////////////////////////////////////
// TRACK METADATA (parsed from new JSON object format)
///////////////////////////////////////////
struct TrackMetadata {
  char longName[32];
  char shortName[16];
  char defaultCourse[MAX_LAYOUT_LENGTH];
  float courseLengthFt[MAX_LAYOUTS];  // per-course lengthFt
  bool isSprint;  // track-level "type": "sprint" (redundant with the folder,
                  // cheap validation that a file landed where it claims)
};

#endif
