TheAngryRaven/DovesDataLogger/BirdsEye/tach_filter.h

#pragma once

#include <stdint.h>

///////////////////////////////////////////
// TACHOMETER KALMAN FILTER
// The 1-D Kalman filter that turns mean inter-pulse periods into a
// smoothed RPM estimate, extracted from tachometer.ino so the math is
// host-testable. The ISR/ring-buffer plumbing stays in the sketch; this
// unit owns the predict/update equations and the tuning constants.
//
// Pure logic — no Arduino headers — so it is exercised by host tests.
//
// WHERE THE SPIKES CAME FROM (plan 0009). The estimator only ever saw
// ONE number per pulse — the RPM implied by that period — and folded it
// in with a steady-state gain of ~0.43. So a single bad edge (ignition
// ringing sneaking past the debounce, or a spark the pickup missed) is
// not a small error: at 3000 RPM a spurious edge 4 ms after a real one
// reads as 15 000 RPM, and 43% of that lands in the output. That is a
// 5000 RPM spike from ONE bad microsecond reading, and nothing in the
// pipeline could tell it apart from a real engine speed. Three changes
// fix it, all in this unit:
//
//   1. An OUTLIER GATE. A measurement further than kGateSigmas from the
//      estimate is not folded in — the estimate coasts instead. Three
//      consecutive rejections mean the estimate, not the measurement, is
//      wrong, so the third one is adopted outright.
//   2. MEASUREMENT NOISE THAT KNOWS THE RPM. RPM = K / period, so a
//      fixed timing error is worth RPM^2/K of RPM error — quadratic. A
//      flat 2500 RPM^2 was roughly right at 4000 RPM and far too
//      confident above 8000, which is why the trace got noisier the
//      harder the engine was working.
//   3. PROCESS NOISE PER SECOND, not per update. Updates arrive at the
//      pulse rate, so a per-update Q made the filter four times looser
//      at 12 000 RPM than at 3000 — and looser again whenever an SD
//      stall batched several pulses into one update.
///////////////////////////////////////////

namespace tach_filter {

///////////////////////////////////////////
// FILTER MODE (plan 0009)
//
// Exposed as the `tach_filter` setting so the filter can be A/B'd against
// a live engine at the track instead of argued about from a plotted log.
///////////////////////////////////////////
enum class Mode : uint8_t {
  kSmooth = 0,  // default: time-based Q, RPM-aware R, outlier gate
  kLegacy = 1,  // the pre-0009 filter exactly: fixed Q/R, no gate
  kRaw    = 2,  // no estimator at all — publish what the periods say
};

// Parse the `tach_filter` setting. Unknown/blank/garbled degrades to
// kSmooth, the house idiom: a bad settings value must never be the
// reason a device logs worse data than the shipped default.
Mode modeFromSetting(const char* value);

// Lowercase setting-token name ("smooth" / "legacy" / "raw") — debug logs.
const char* modeName(Mode m);

// One-character tag ('S' / 'L' / 'R') for the 21-column display line.
char modeTag(Mode m);

// Process noise Q for kLegacy: how much RPM^2 the true value can change
// between UPDATES. Kept only so kLegacy reproduces the shipped filter
// bit for bit; kSmooth uses the rate below instead.
constexpr float kProcessNoiseQ = 800.0f;

// Process noise as a RATE (RPM^2 per second), which is what a random-walk
// model actually needs: updates arrive at the pulse rate, so charging a
// fixed Q per update silently retunes the filter with engine speed. The
// value is the legacy Q divided by the 10 ms period of a 6000 RPM single
// — i.e. kSmooth behaves like the old filter at 6000 RPM and, unlike it,
// keeps behaving that way everywhere else.
constexpr float kProcessNoiseRate = 80000.0f;

// Never predict more than this far ahead in one step. A batch that spans
// a long coast (or a sanity-bounded 2 s period) must not open the
// uncertainty so wide that the outlier gate stops meaning anything.
constexpr float kMaxPredictSeconds = 0.5f;

// Floor under the per-update process noise, so a degenerate dt can't
// freeze the filter by driving the Kalman gain to zero.
constexpr float kProcessNoiseFloorQ = 25.0f;

// Measurement noise R base: the RPM-independent floor (~50 RPM std dev).
// Scales inversely with the number of periods in the measurement —
// more pulses, more confidence.
constexpr float kMeasurementNoiseRBase = 2500.0f;

// Fixed per-edge timing uncertainty, microseconds: GPIOTE ISR latency
// (the handler is deferred by SoftDevice radio ISRs like everything else
// at app priority) plus edge-shape variation in the pickup. It costs
// sigma_T * RPM^2 / K of RPM error — 26 RPM at 6000, 143 at 14 000.
constexpr float kTimingJitterUs = 80.0f;
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
